cortesnoel/pixel-art/assets/img/Pixel_Concept_Art_No_Bkg.png

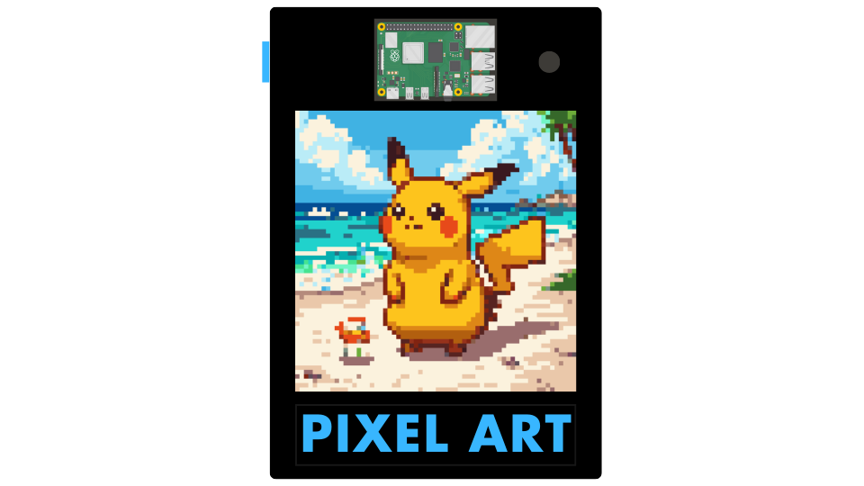
assets/img/Pixel_Concept_Art_No_Bkg.png
